SolderedElectronics/I2C-LCD-driver-board-hardware-design/OUTPUTS/V1.2.2/I2C LCD driver board Pinout.jpg

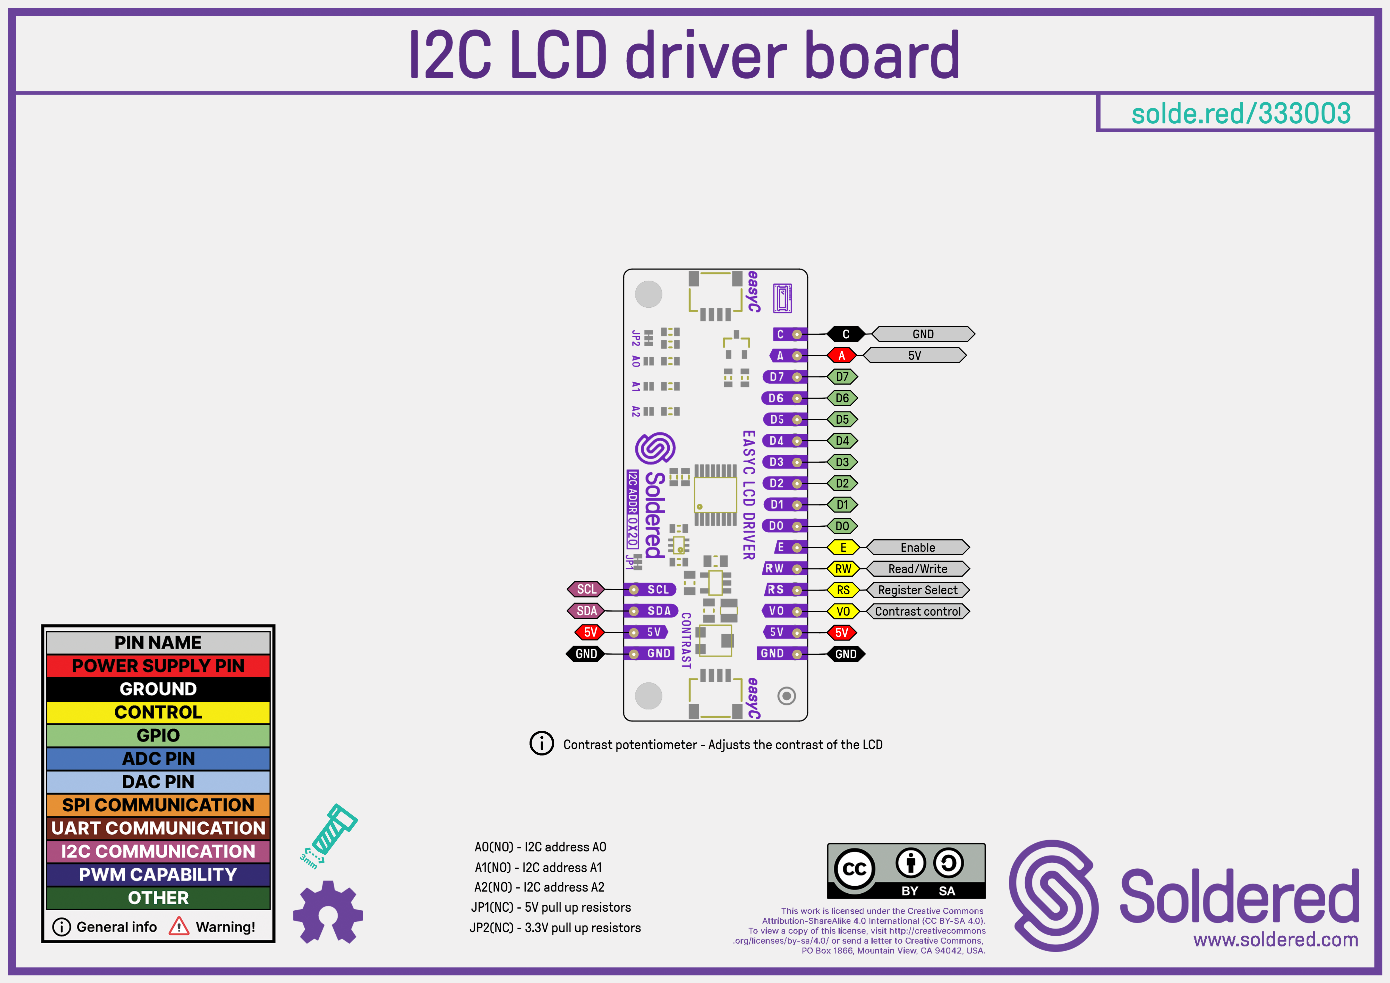
OUTPUTS/V1.2.2/I2C LCD driver board Pinout.jpg
